devriesewouter89/CoGhentToiletPaper/3DPrint/Camera/Arm_3.stl

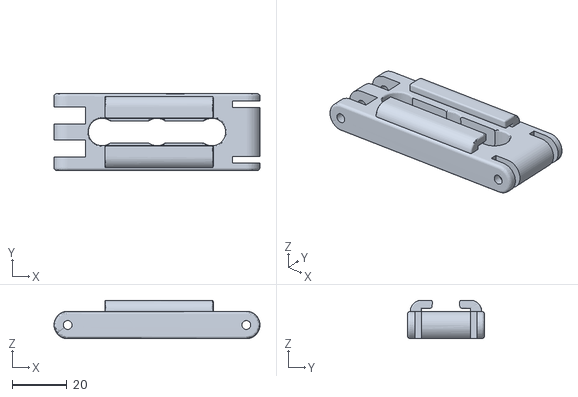
[picture p33: CAD file, 2023-06-02]
3DPrint/Camera/Arm_3.stl
75.0 x 28.0 x 14.0
