devriesewouter89/CoGhentToiletPaper/3DPrint/roll_fixation/paper_roll_side/nema17_toilet_fixation_2.stl

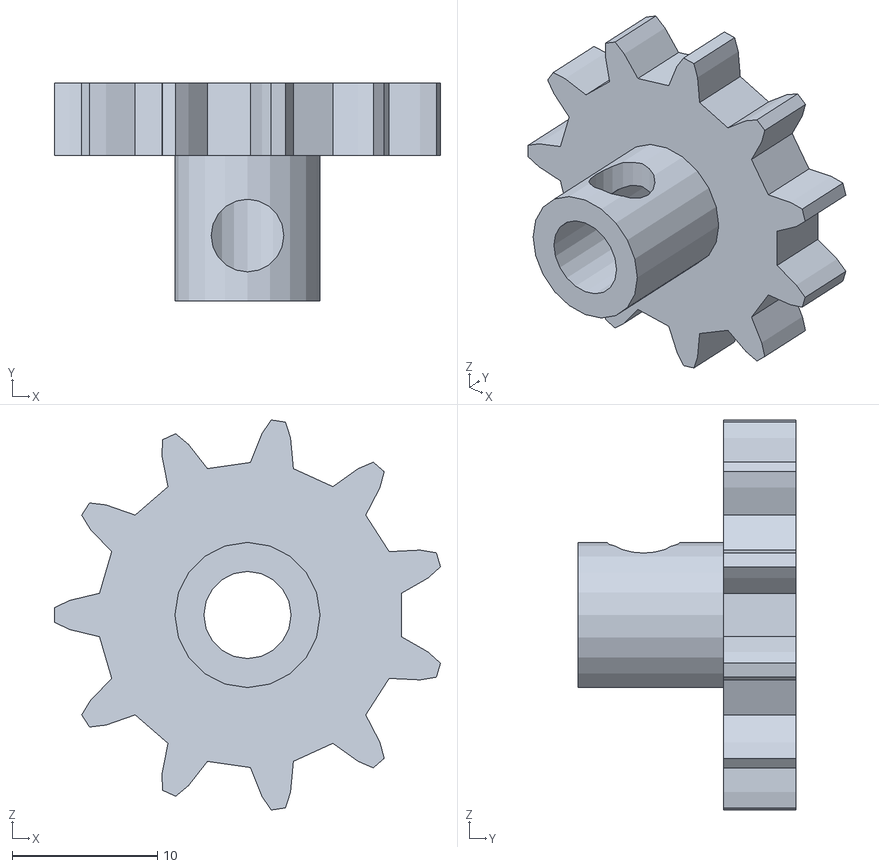
[picture p34: CAD file, 2023-01-07]
3DPrint/roll_fixation/paper_roll_side/nema17_toilet_fixation_2.stl
26.6 x 15.0 x 26.9
