devriesewouter89/CoGhentToiletPaper/physical_construct/3DPrint/roll_fixation/grabber_side/toilet_grabber_insert_small.stl

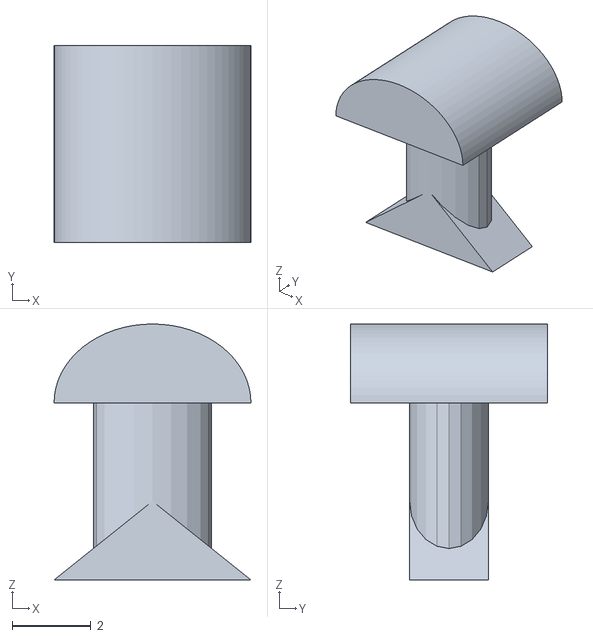
[picture p35: CAD file, 2023-05-21]
physical_construct/3DPrint/roll_fixation/grabber_side/toilet_grabber_insert_small.stl
5.00 x 5.00 x 6.50
