devriesewouter89/CoGhentToiletPaper/3DPrint/Camera/Arm_1.stl

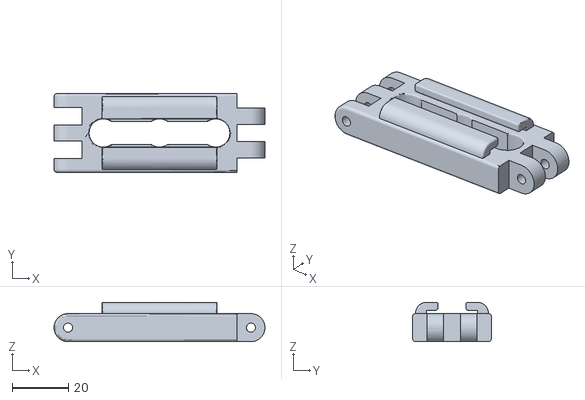
[picture p36: CAD file, 2023-06-02]
3DPrint/Camera/Arm_1.stl
75.0 x 28.0 x 14.0
