devriesewouter89/CoGhentToiletPaper/physical_construct/3DPrint/roll_fixation/grabber_side/toilet_grabber.stl

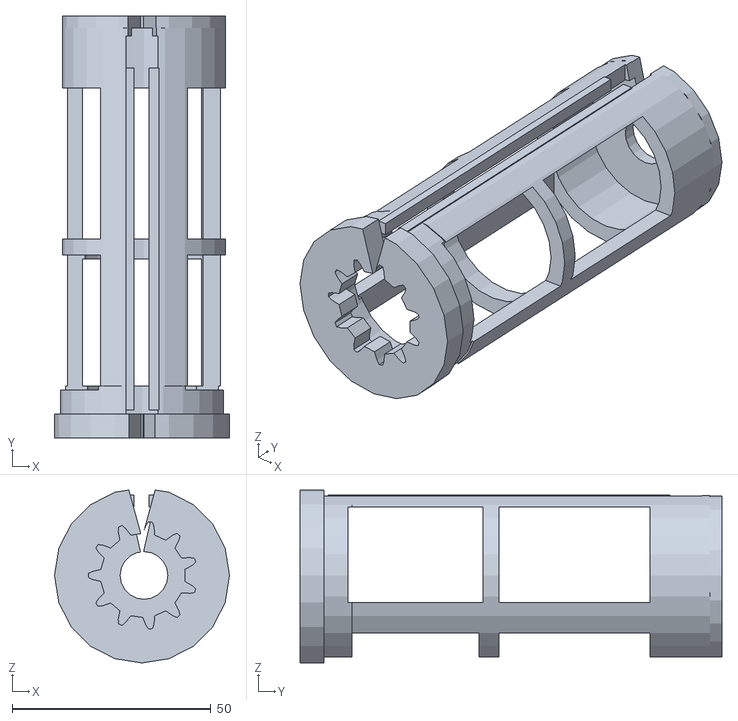
[picture p37: CAD file, 2023-01-21]
physical_construct/3DPrint/roll_fixation/grabber_side/toilet_grabber.stl
44.0 x 106.0 x 43.5
