devriesewouter89/CoGhentToiletPaper/3DPrint/Camera/Camera_frontplate.stl

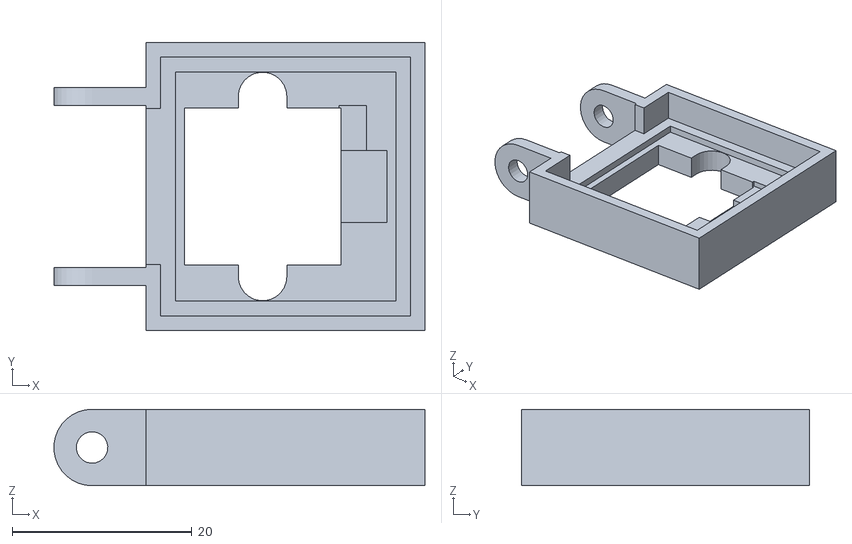
[picture p38: CAD file, 2023-06-02]
3DPrint/Camera/Camera_frontplate.stl
41.2 x 32.0 x 8.50
