devriesewouter89/CoGhentToiletPaper/physical_construct/3DPrint/roll_fixation/grabber_side/toilet_grabber_insert.stl

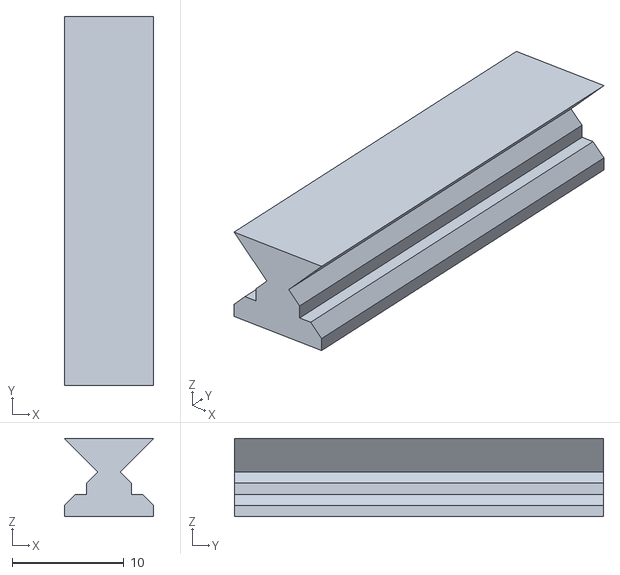
[picture p39: CAD file, 2023-01-07]
physical_construct/3DPrint/roll_fixation/grabber_side/toilet_grabber_insert.stl
8.00 x 33.0 x 7.00
