devriesewouter89/CoGhentToiletPaper/src/physical_control/toilet_paper_placement_indicator/template_matching.py

#!/usr/bin/python3

import atexit
import os
import time
from enum import Enum

import cv2
from picamera2 import Picamera2
from picamera2.encoders import H264Encoder

from src.config_toilet import get_git_root, Config
import argparse

class PLACEMENT(Enum):
    NOT_FAR = 0
    CORRECT = 1
    TOO_FAR = 2


class CamControl:
    def __init__(self, config):
        self.config = config
        self.register()
    def register(self):
        self.picam2 = Picamera2()
        self.video = False
        # half_resolution = [dim // 2 for dim in picam2.sensor_resolution]
        half_resolution = (640, 480)
        # Encode a VGA stream, and capture a higher resolution still image half way through.
        main_stream = {"size": half_resolution}
        lores_stream = {"size": (640, 480)}
        self.video_config = self.picam2.create_video_configuration(main_stream, lores_stream, encode="lores")
        self.preview_config = self.picam2.create_preview_configuration(main={"size": half_resolution})
        atexit.register(self.close)

    def start_vid_rec(self):
        if(self.picam2==None):
            self.register()
        self.picam2.configure(self.video_config)
        encoder = H264Encoder(10000000)
        self.picam2.start_recording(encoder, 'test.h264')
        self.video = True
        time.sleep(2)

    def stop_vid_rec(self):
        self.picam2.stop_recording()
        self.video = False

    def capture_during_rec(self):
        if not self.video:
            self.start_vid_rec()
        request = self.picam2.capture_request()
        request.save("main", str(self.config.temp_img.resolve()))
        request.release()
        return

    def capture_jpeg(self):

        self.picam2.configure(self.preview_config)
        # self.picam2.start_preview(Preview.QTGL)
        self.picam2.start()
        time.sleep(2)
        metadata = self.picam2.capture_file(str(self.config.prep_img.resolve()))
        #print(metadata)
        self.picam2.stop()

    def close(self):
        self.picam2.close()


class SheetPlacement():
    def __init__(self, cc: CamControl, config: Config):
        self.cc = cc
        self.config = config
        self.template = cv2.imread(str(self.config.template.resolve()), 0)
        self.region_of_ok = self.config.region_of_interest

    def prepare(self):
        # capture image
        self.cc.capture_jpeg()
        # create template
        template = self.create_template()
        # create region where the paper lies correctly
        region_of_ok = self.create_region_of_interest(str(self.config.prep_img.resolve()), "region of ok")
        config_path = os.path.join(get_git_root(os.getcwd()), "config_toilet.py")

        self.save_region_of_interest(config_path, region_of_ok)
        return template, region_of_ok

    def qualify_position(self, input_image: str, template, region_of_ok):

        overlay, max_loc, max_val = self.return_matched_image(input_image, template)
        
        # print("region of ok {}".format(region_of_ok))
        if (region_of_ok[0] < max_loc[0] < region_of_ok[0] + region_of_ok[2]) & (max_val >= self.config.location_threshold):
            print("OK")
            #cv2.imshow("overlay", cv2.resize(overlay, (int(overlay.shape[1] * 0.6), int(overlay.shape[0] * 0.6))))
            #cv2.waitKey(0)
            #cv2.destroyAllWindows()
            return PLACEMENT.CORRECT
        else:
            # todo right now I start with not far, as otherwise we keep returning to the same page,
            # todo ?how to tackle this problem?
            # todo perhaps check the distance of too far at start and have the paper move out of sight, only then enable
            # todo the option TOO FAR again?
            return PLACEMENT.NOT_FAR
            # if max_loc[0] > region_of_ok[0] + region_of_ok[2]:
            #     print("Not far")
            #     return PLACEMENT.NOT_FAR
            # else:
            #     print("Too far")
            #     return PLACEMENT.TOO_FAR

    def open_stream_until_OK(self, template, region_of_ok):
        self.cc.start_vid_rec()
        result = PLACEMENT.NOT_FAR
        while result != PLACEMENT.CORRECT:
            # It's better to capture the still in this thread, not in the one driving the camera.
            self.cc.capture_during_rec()
            result = self.qualify_position(str(self.config.temp_img.resolve()), template, region_of_ok)

        # time.sleep(5)
        self.cc.stop_vid_rec()

    def check_placement_via_pic(self):
        self.cc.capture_jpeg()
        img_to_verify = str(self.config.prep_img.resolve())
        placement = self.qualify_position(img_to_verify, self.template, self.region_of_ok)
        return placement

    def create_template(self):
        '''
        This code will first convert the template image to grayscale, which is necessary for some image processing operations.
        It will then apply a bilateral filter to the grayscale image to improve the contrast and remove noise.
        Finally, it will threshold the filtered image to create a binary image, which is a simple representation of the template
        image with only two pixel values (0 and 255).

        You can adjust the parameters of the bilateral filter and the thresholding operation to suit the specific needs of your
        template image. For example, you may need to adjust the values of sigmaColor and sigmaSpace in the call
        to cv2.bilateralFilter to achieve the desired level of noise reduction. Similarly, you may need to adjust the
        value of threshold in the call to cv2.threshold to achieve the desired level of binarization.
        @param img:
        @return:
        '''

        # define the region of interest
        roi = self.create_region_of_interest(str(self.config.prep_img.resolve()), "template creation")

        # crop the image
        cropped_template = self.cropped_img_via_roi(str(self.config.prep_img.resolve()), roi)

        # Convert the template image to grayscale
        gray_template = cv2.cvtColor(cropped_template, cv2.COLOR_BGR2GRAY)

        # Apply image filtering to improve the contrast and remove noise
        filtered_template = cv2.bilateralFilter(gray_template, 2, 25, 75)

        # Threshold the image to create a binary image
        ret, thresh = cv2.threshold(filtered_template, 180, 255, cv2.THRESH_BINARY)

        # Display the result
        # cv2.imshow('cropped template', cropped_template)
        # cv2.imshow('gray_template', gray_template)
        # cv2.imshow('filtered_template', filtered_template)
        # cv2.imshow('thresh', thresh)
        cv2.imwrite(str(self.config.template.resolve()), thresh)
        cv2.waitKey(0)
        cv2.destroyAllWindows()
        return thresh

    def test_roi(self):
        img = os.path.join(os.getcwd(), "1.jpg")
        print(img)
        roi = self.create_region_of_interest(img)
        imCrop = self.cropped_img_via_roi(img, roi)
        # Display cropped image
        cv2.imshow("Image", imCrop)
        cv2.waitKey(0)
        # test roi on other images:
        img2 = os.path.join(os.getcwd(), "2.jpg")
        imCrop = self.cropped_img_via_roi(img2, roi)
        # Display cropped image
        cv2.imshow("Image", imCrop)
        cv2.waitKey(0)
        cv2.destroyAllWindows()

    def cropped_img_via_roi(self, img, roi):
        '''
        crop an image
        @param img:
        @param roi:
        @return:
        '''
        # Read image
        im = cv2.imread(img)
        # Crop image
        imCrop = im[int(roi[1]):int(roi[1] + roi[3]), int(roi[0]):int(roi[0] + roi[2])]
        return imCrop

    def create_region_of_interest(self, img, window_name: str = ""):
        # Read image
        im = cv2.imread(img)

        # Select ROI
        r = cv2.selectROI(window_name, im)
        cv2.destroyAllWindows()

        return r

    def save_region_of_interest(self, config_path: str, region_of_interest):
        with open(config_path, 'r', encoding='utf-8') as file:
            data = file.readlines()
        line_to_change = None
        for idx, i in enumerate(data):
            if "region_of_interest" in i:
                line_to_change = idx
        data[line_to_change] = "    region_of_interest = {}\r\n".format(region_of_interest)

        with open(config_path, 'w', encoding='utf-8') as file:
            file.writelines(data)

    def return_matched_image(self, input_image_path: str, template, min_height=0, max_height=3840):
        input_image = cv2.imread(input_image_path, 0)
        # cv2.imshow("input normal", input_image)
        # cv2.waitKey(0)
        # cv2.destroyAllWindows()
        # # todo change with roi
        input_image = input_image[min_height: max_height, 0: input_image.shape[1]]

        # cv2.imshow("input cropped", input_image)
        # Perform template matching
        result = cv2.matchTemplate(input_image, template, cv2.TM_CCOEFF_NORMED)

        # Find the coordinates of the best match
        min_val, max_val, min_loc, max_loc = cv2.minMaxLoc(result)

        # Extract the region of the input image that contains the notch
        h, w = template.shape
        top_left = max_loc
        bottom_right = (top_left[0] + w, top_left[1] + h)
        cropped = input_image[top_left[1]:bottom_right[1], top_left[0]:bottom_right[0]]
        orig_image = cv2.imread(input_image_path)
        orig_image = orig_image[min_height: max_height, 0: input_image.shape[1]]
        overlay = cv2.rectangle(orig_image.copy(), max_loc, (max_loc[0] + w, max_loc[1] + h), (0, 0, 255), 2)
        print("coordinates of max loc: {} with certainty {}".format(max_loc, max_val))
        # Display the result for debugging
        # cv2.imshow("overlay", overlay)
        # cv2.waitKey(0)
        # cv2.destroyAllWindows()
        return overlay, max_loc, max_val


'''
This code will perform template matching using the method cv2.TM_CCOEFF_NORMED, which computes the normalized 
cross-correlation between the template and the input image. It will then find the coordinates of the best match 
and extract the region of the input image that contains the notch. Finally, it will display the template, 
the input image, and the cropped region containing the notch.
'''

if __name__ == '__main__':
    parser = argparse.ArgumentParser(
                    prog='template matching',
                    description='a script to determine of our toilet paper is correctly positioned, by analysing the position of the notches via template matching',
                    epilog="it's all about the toilet paper")
    parser.add_argument('-p', '--prep',
                    action='store_true', help='generate the template')  # on/off flag
    args = parser.parse_args()
    config = Config()
    cc = CamControl(config)
    sheet = SheetPlacement(cc, config)
    manual = False
    prep = args.prep
    if (prep):
        template, region_of_ok = sheet.prepare()
    else:
        # Load the template image and the input image
        region_of_ok = config.region_of_interest
        template = cv2.imread('template.jpg', 0)

    if manual:
        template = cv2.imread('template.jpg', 0)
        # img_path = Path(Path.cwd().parent / "training_init_toilet_roll" / "too_far")
        # img_path = './frames/backlit/NF/0056.png'
        img_path = 'template_matching_test/frames/plexi/backlit/NF/032.png'
        #
        input_image = cv2.imread(img_path, 0)
        overlay, max_loc = sheet.return_matched_image(input_image, template)
        cv2.imshow("overlay", cv2.resize(overlay, (int(overlay.shape[1] * 0.6), int(overlay.shape[0] * 0.6))))
        cv2.waitKey(0)
        print("region of ok {}".format(region_of_ok))
        if region_of_ok[0] < max_loc[0] < region_of_ok[0] + region_of_ok[2]:
            print("OK")
        else:
            print("Not OK")
    else:
        sheet.open_stream_until_OK(template, region_of_ok)
# TODO compare with next methods, perhaps these are better?
# https://github.com/cozheyuanzhangde/Invariant-TemplateMatching
# https://github.com/DennisLiu1993/Fastest_Image_Pattern_Matching
